facebookarchive/RiftDK2/Headset/Optical/DK2_Optical_Design.pdf

# DK2 Optical Design

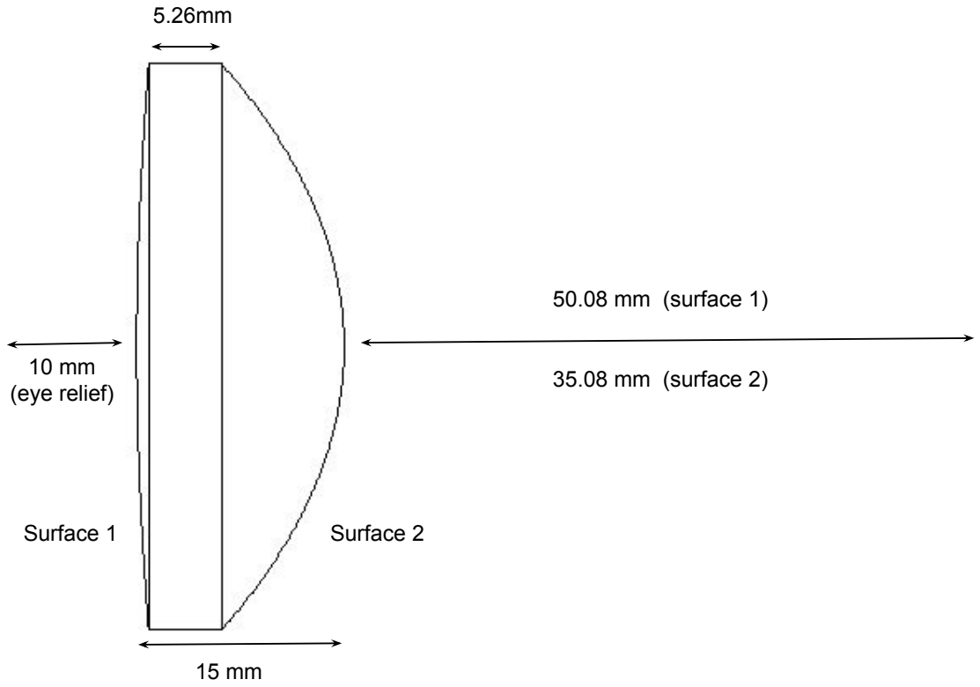
[picture p18: figure]
Surface 1; Surface 2; 10 mm (eye relief); 50.08 mm (surface 1); 35.08 mm (surface 2)

Material: Polycarbonate
Surface 1: radius = 20.457 mm, curvature radius = 212.774, conic = -60.6277 Surface 2: radius = 20.457 mm, curvature radius = -24.2189, conic = -0.863502 Thickness: 15 mm
Stereo Lens Separation: 63.5 mm
Active Screen Size: 125.76 x 70.74 mm (1920 x 1080 pixels)
Optical Center Screen Position: Left = (31.13, 35.37) mm | Right = (94.63, 35.37) mm ⁴⁰.914 mm

Active screen (not including front glass)
