facebookarchive/RiftDK2/Documentation/Figures/image6-25.png

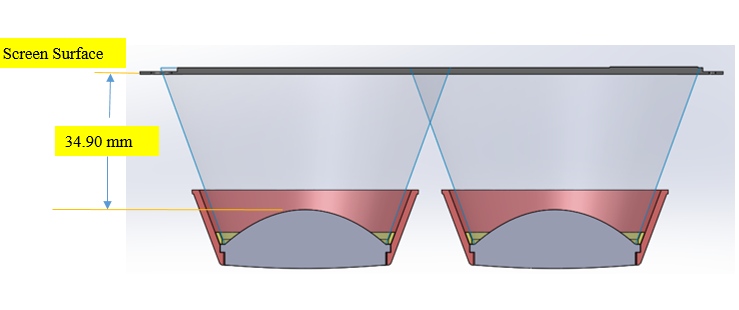
Documentation/Figures/image6-25.png
