facebookarchive/RiftDK2/Headset/Artwork/DK2 artwork placement Development Kit 2.PDF

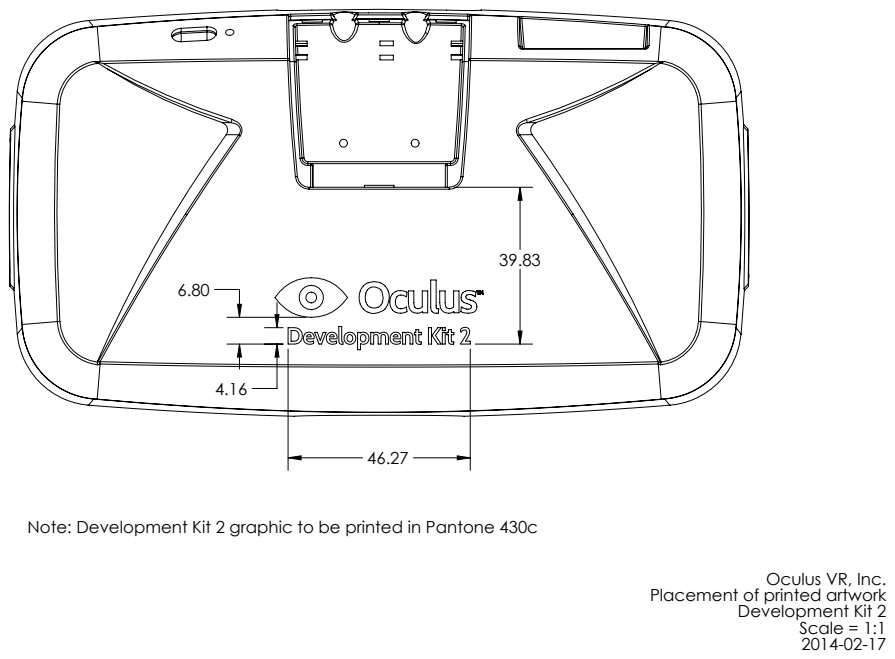
[picture p43: page 1]

Note: Development Kit 2 graphic to be printed in Pantone 430c

Oculus VR, Inc.
Development Kit 2
Scale = 1:1

Placement of printed artwork
