facebookarchive/RiftDK2/Headset/Artwork/DK2 master carton 2014-06-12.pdf

834 | 313

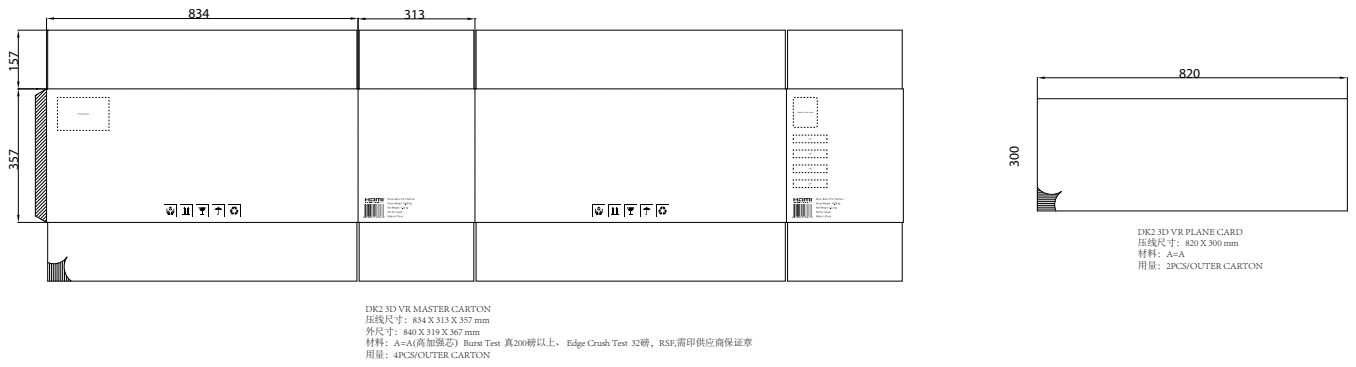
[picture p44: page 1]

DK2 3D VR PLANE CARD
压线尺寸：820 X 300 mm
用量：2PCS/OUTER CARTON

DK2 3D VR MASTER CARTON
压线尺寸：834 X 313 X 357 mm
外尺寸：840 X 319 X 367 mm
材料：A=A(高加强芯）Burst Test 真200磅以上、 Edge Crush Test 32磅，RSF,需印供应商保证章
用量：4PCS/OUTER CARTON
