facebookarchive/RiftDK2/Headset/Artwork/DK2 overpack 2014-06-12.pdf

280.0

295 | 199

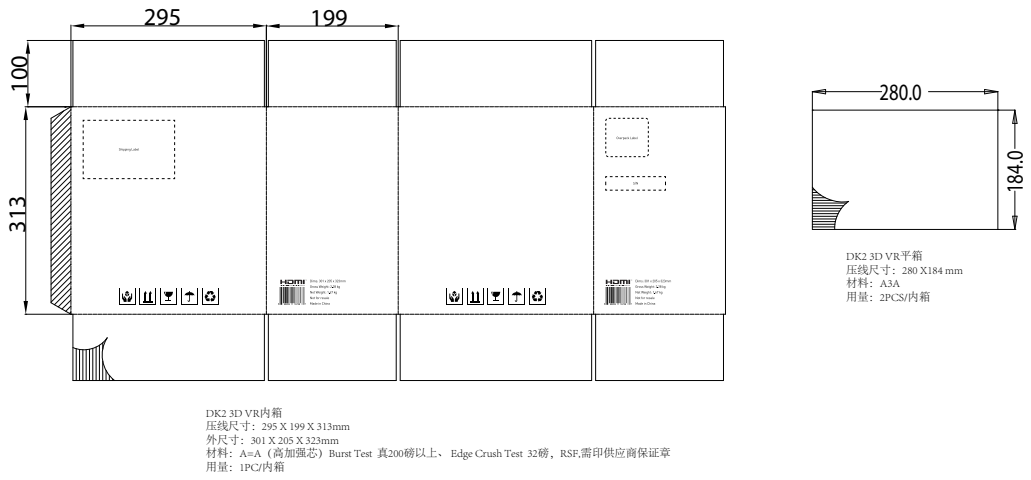
[picture p45: page 1]
DK2 3D VR平箱 压线尺寸：280 X184 mm 材料：A3A 用量：2PCS/内箱

DK2 3D VR内箱
压线尺寸：295 X 199 X 313mm
外尺寸：301 X 205 X 323mm
材料：A=A（高加强芯）Burst Test 真200磅以上、 Edge Crush Test 32磅，RSF,需印供应商保证章
