facebookarchive/RiftDK2/Headset/Artwork/USB-HDMI-Packaging_1.3.pdf

SCALE 200% | ACTUAL SIZE

# DK2: USB / HDMI SILKSCREEN

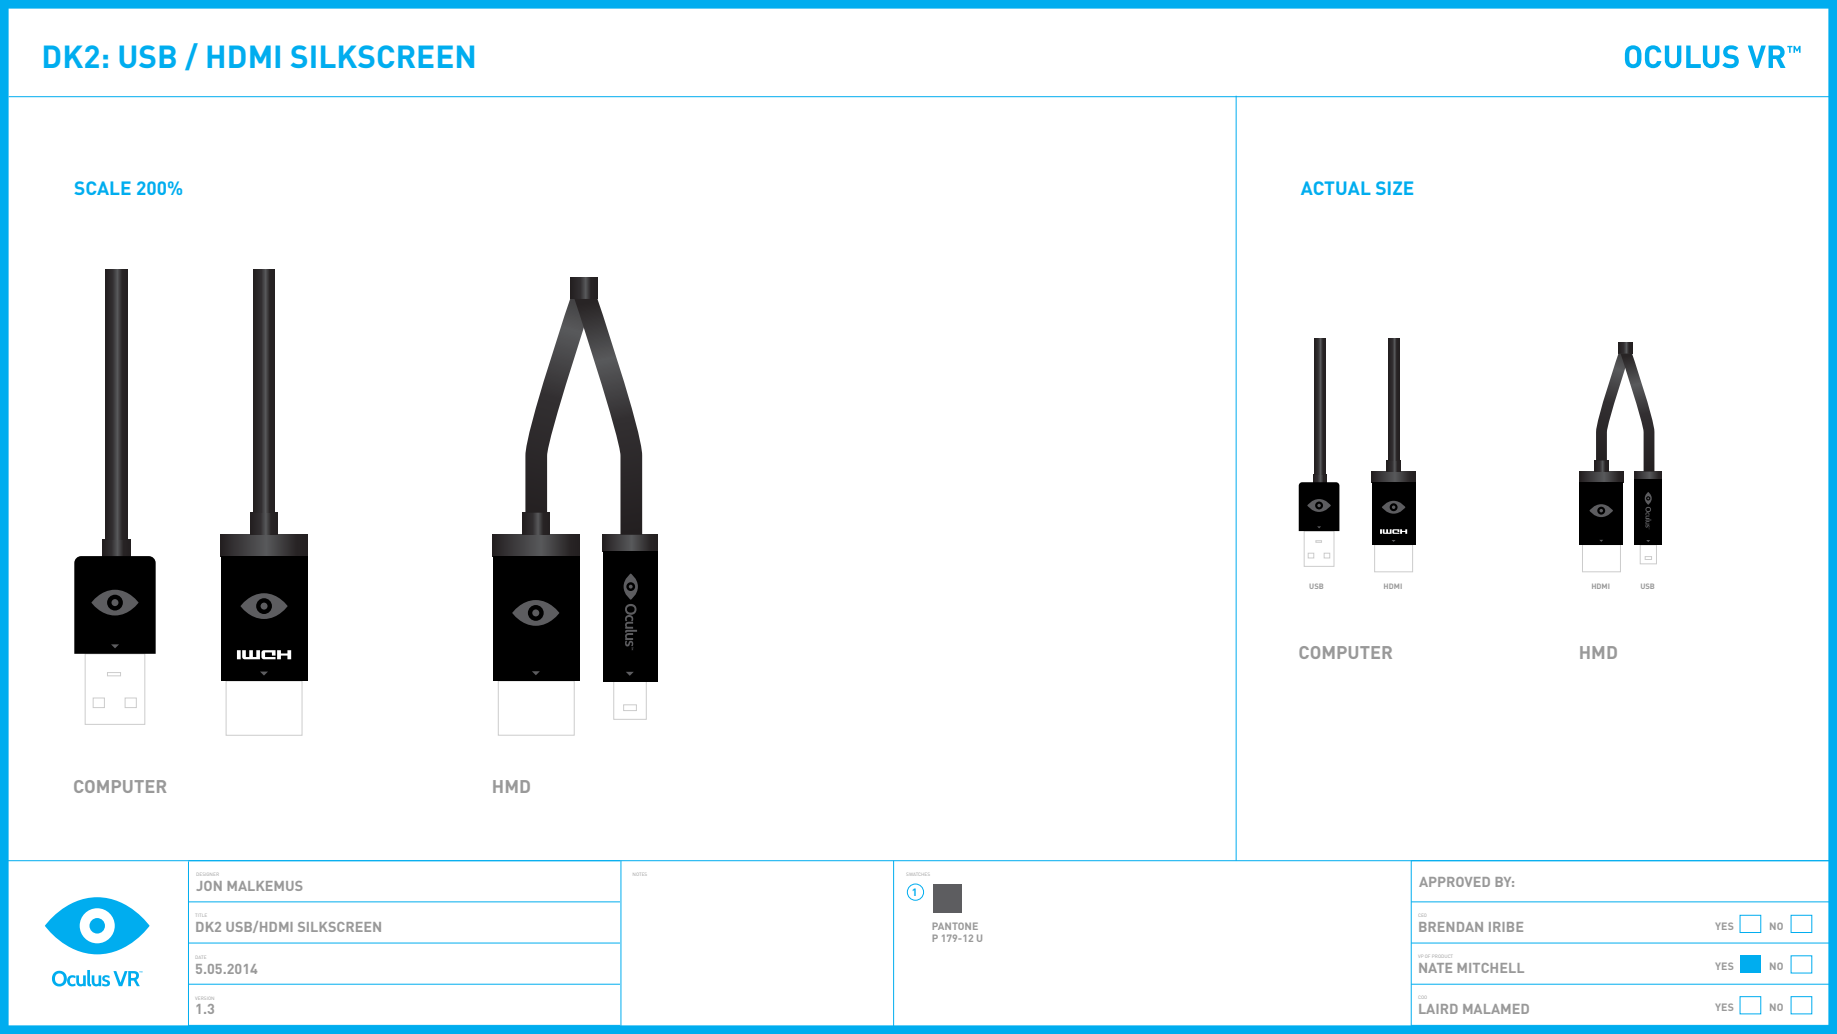
[picture p46: page 1]
COMPUTER; JON MALKEMUS; DESIGNER; NOTES; SWATCHES; DATE; VERSION; APPROVED BY:; BRENDAN IRIBE; YES; CEO; LAIRD MALAMED; COO; HMD; PANTONE P 179-12 U; USB; HDMI

TITLE
DK2 USB/HDMI SILKSCREEN

VP OF PRODUCT
NATE MITCHELL
