facebookarchive/RiftDK2/Headset/Electrical/Mainboard/Release/DK2_REV3.3_SCH.pdf

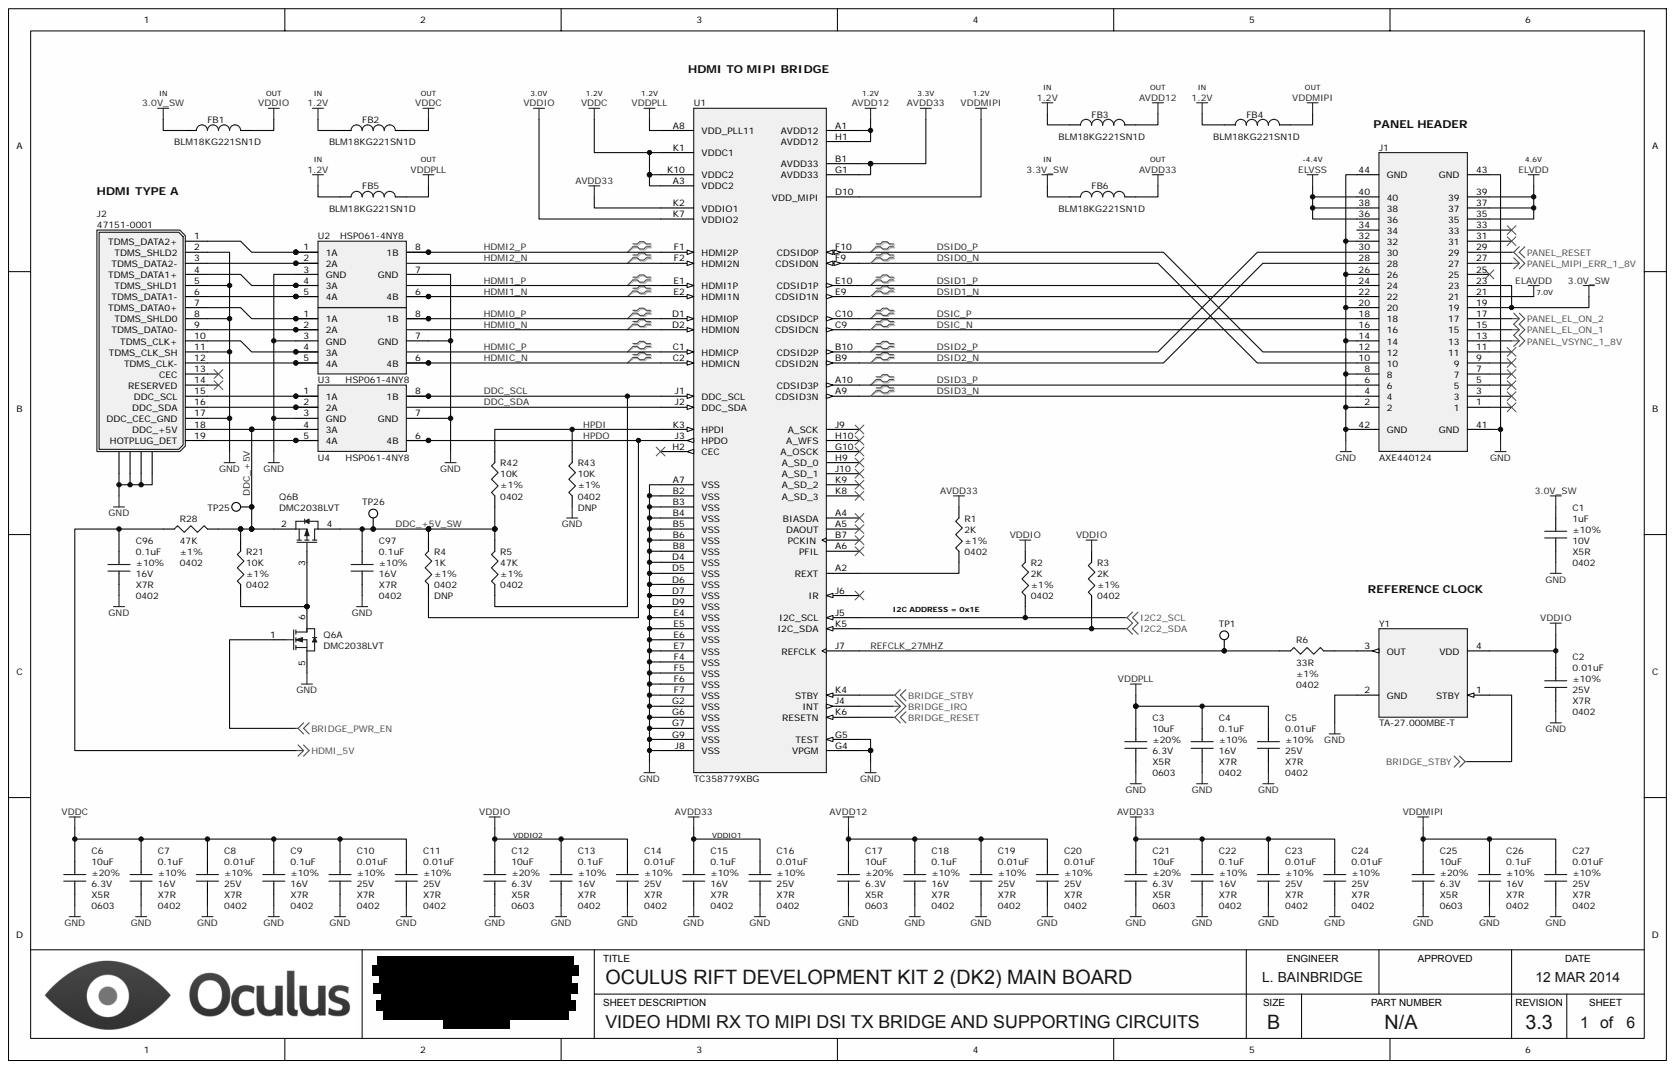
[picture p47: page 1]

HDMI TO MIPI BRIDGE

SHEET DESCRIPTION
VIDEO HDMI RX TO MIPI DSI TX BRIDGE AND SUPPORTING CIRCUITS

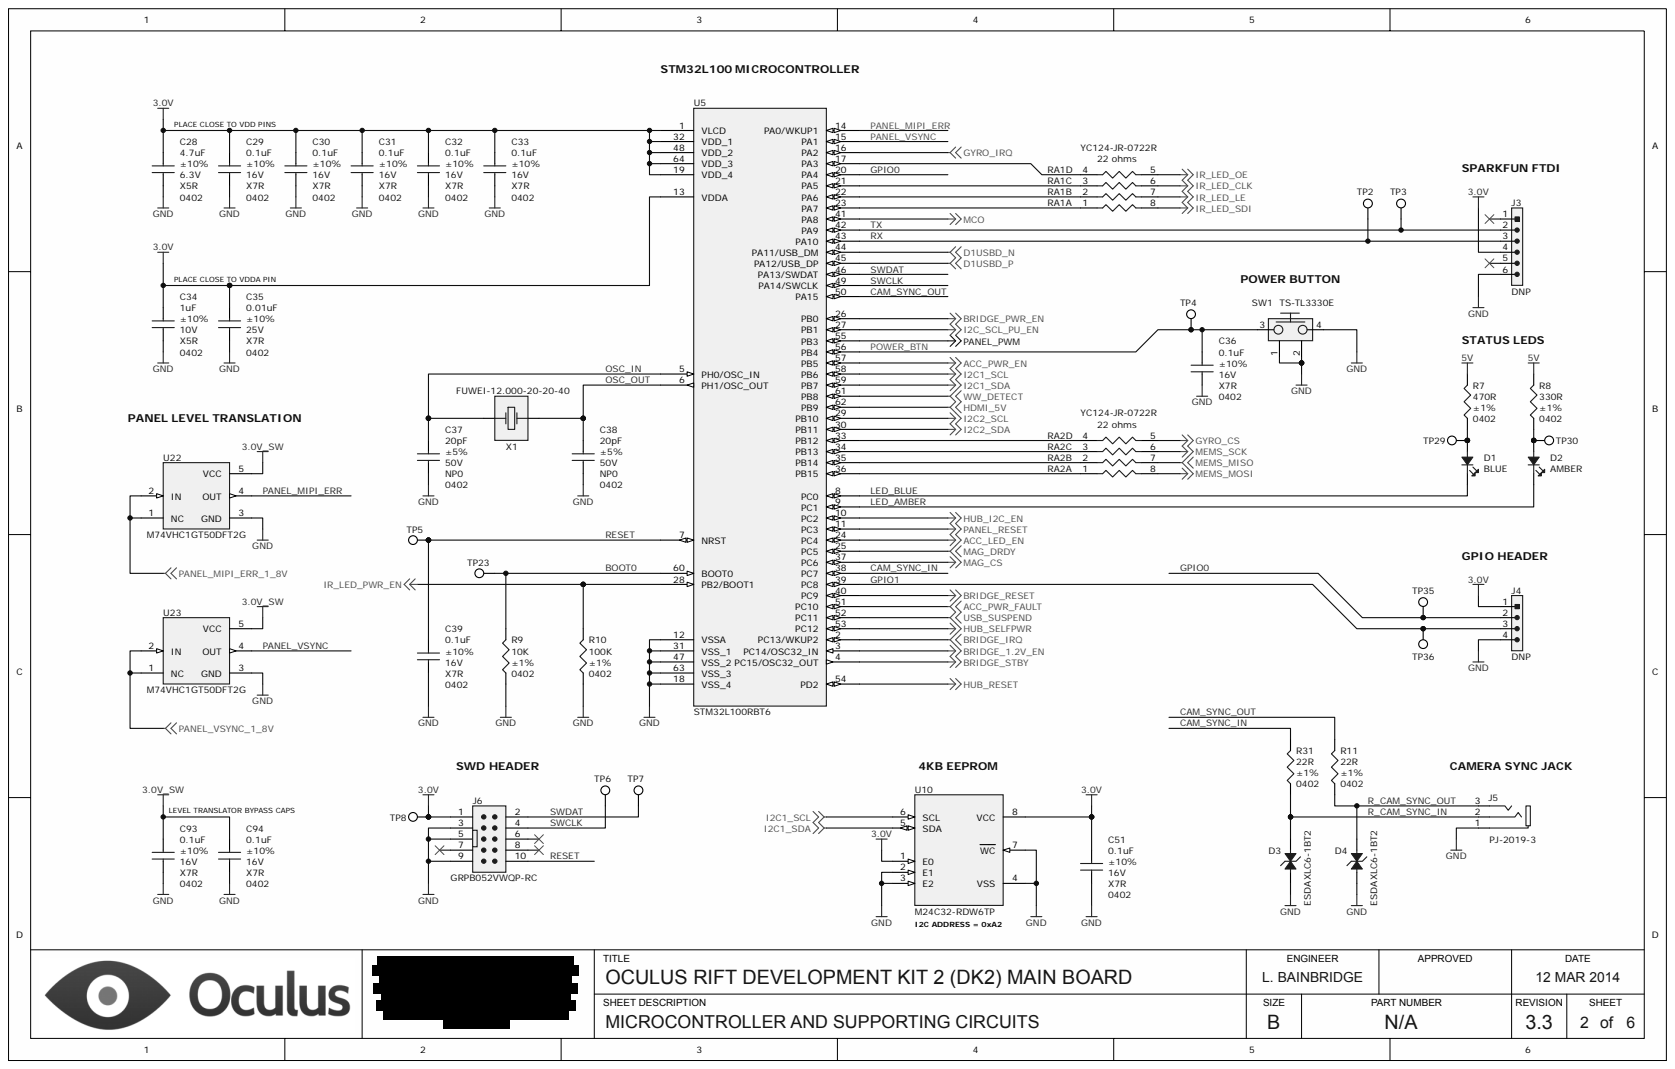
[picture p48: page 2]

MICROCONTROLLER AND SUPPORTING CIRCUITS

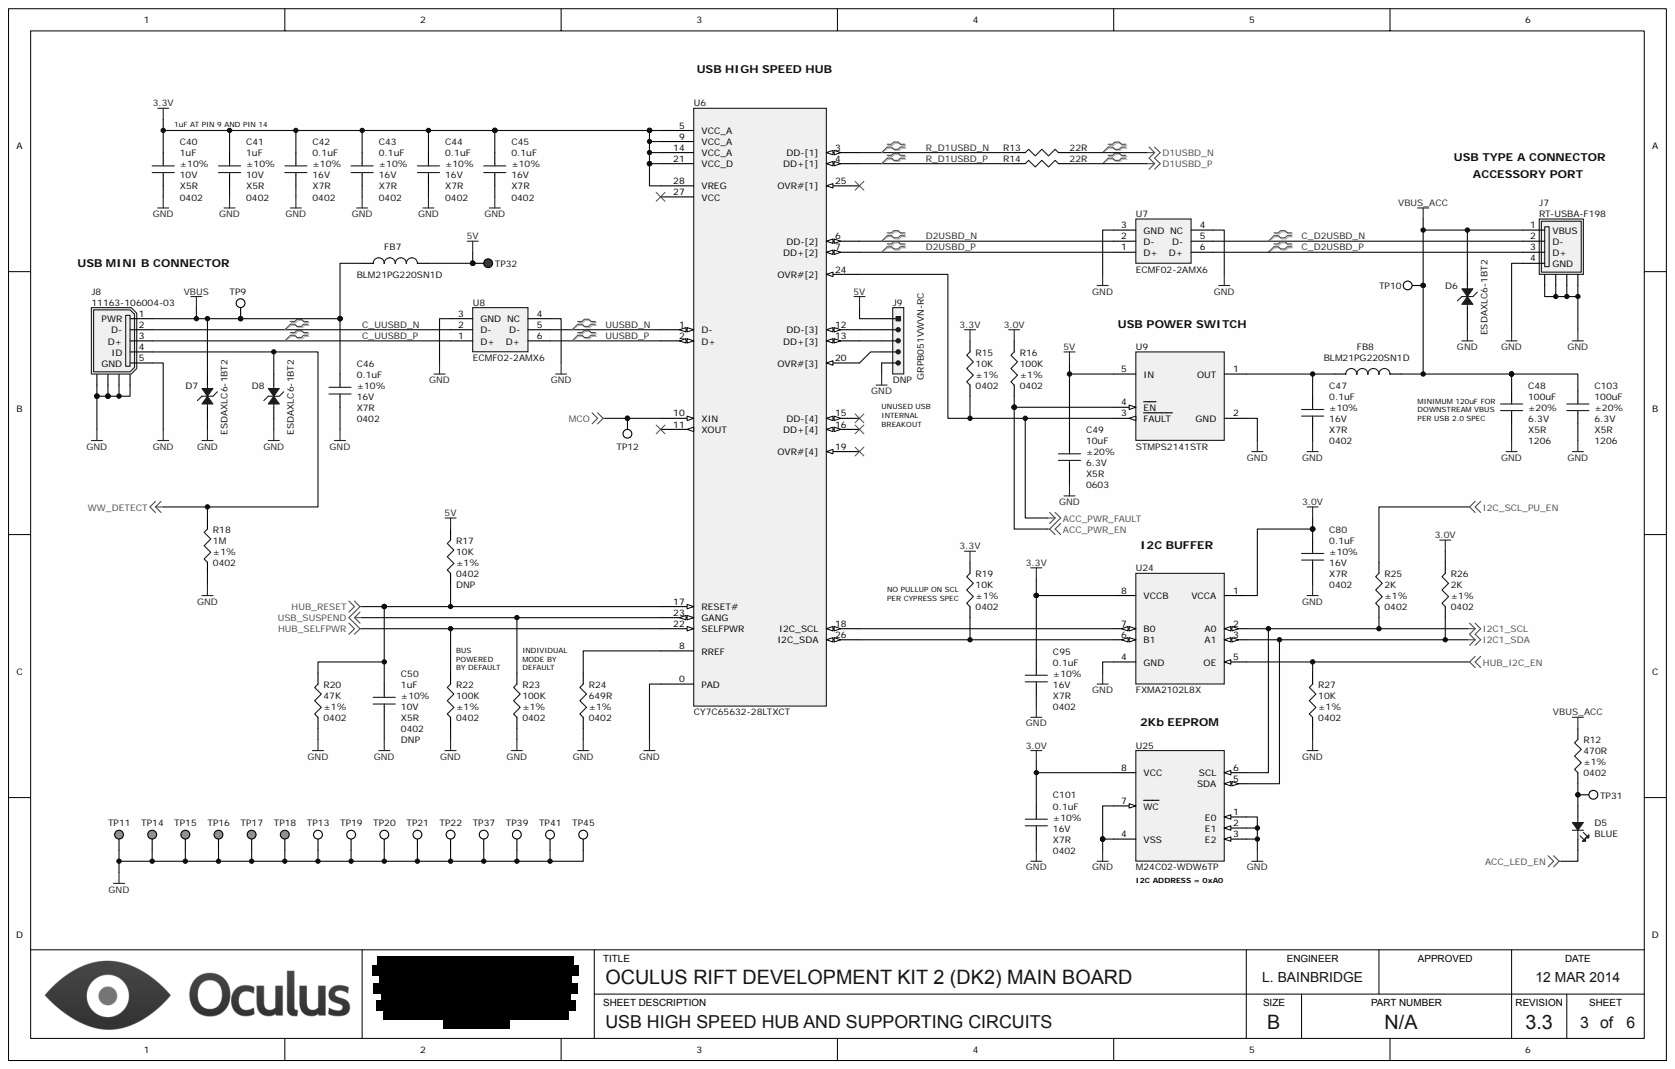
[picture p49: page 3]

USB HIGH SPEED HUB

NO PULLUP ON SCL
PER CYPRESS SPEC

SELFPWR 22 GANG 23

RREF 8 PAD 0

USB HIGH SPEED HUB AND SUPPORTING CIRCUITS

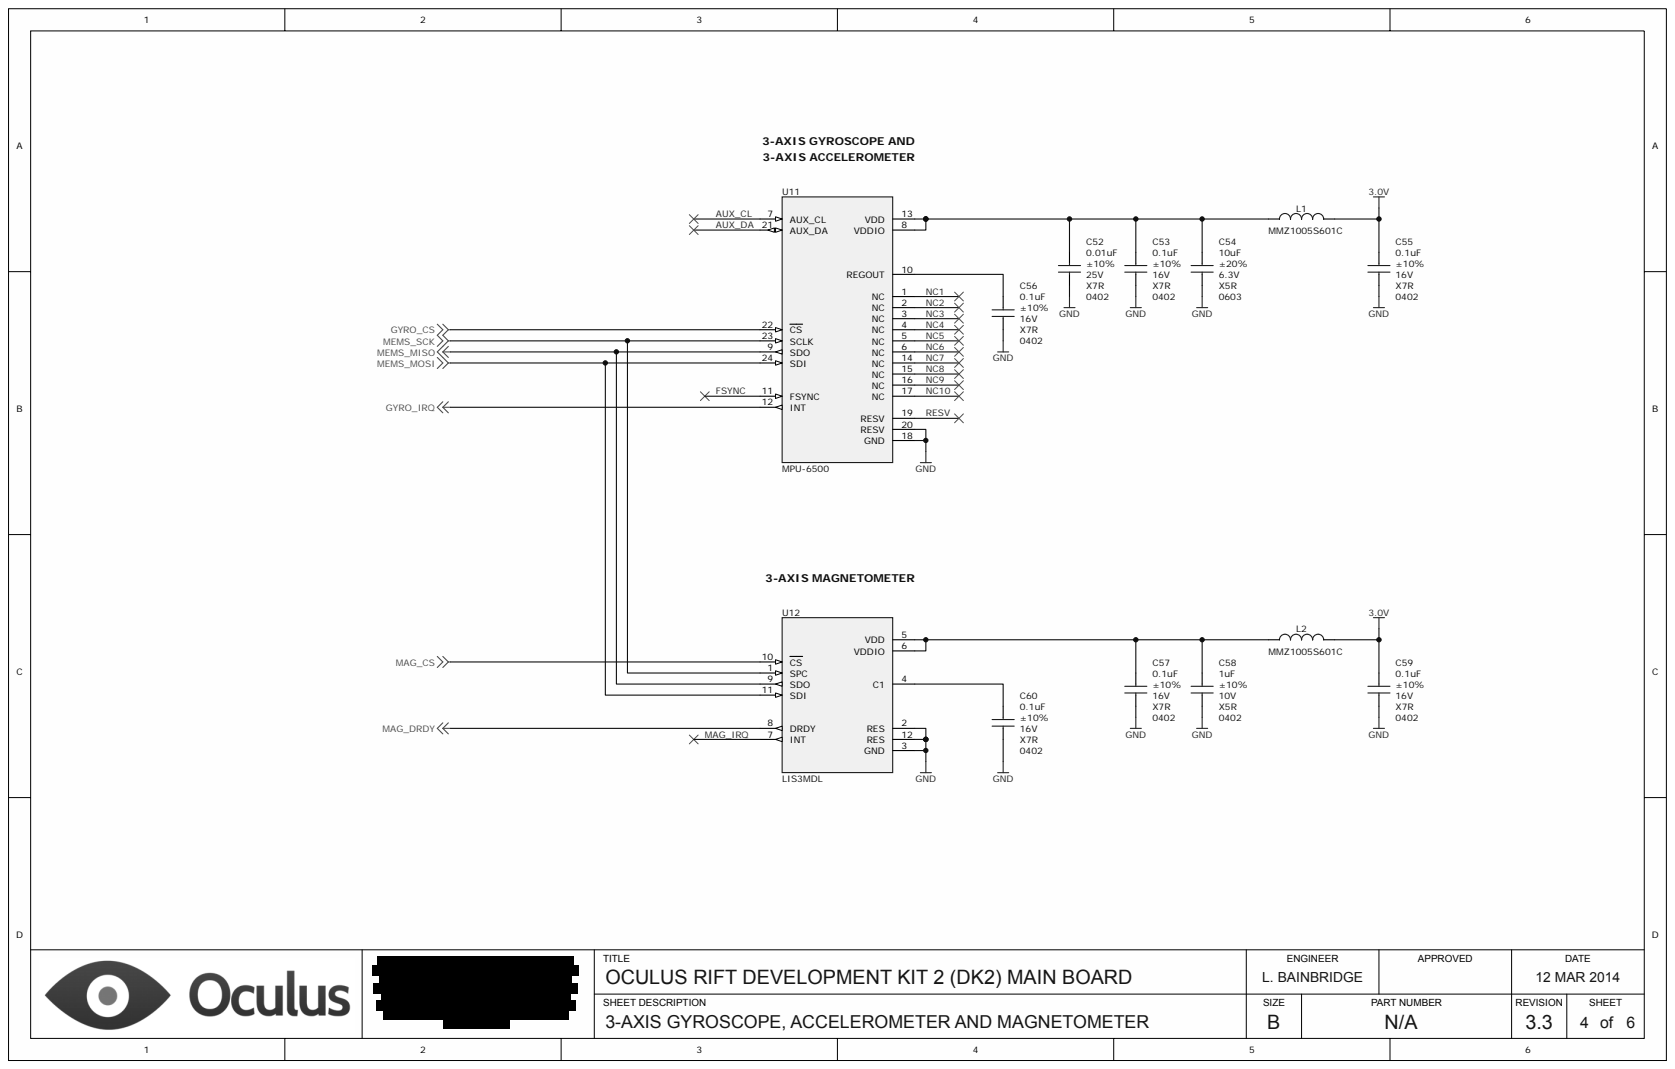
[picture p50: page 4]

3-AXIS GYROSCOPE, ACCELEROMETER AND MAGNETOMETER

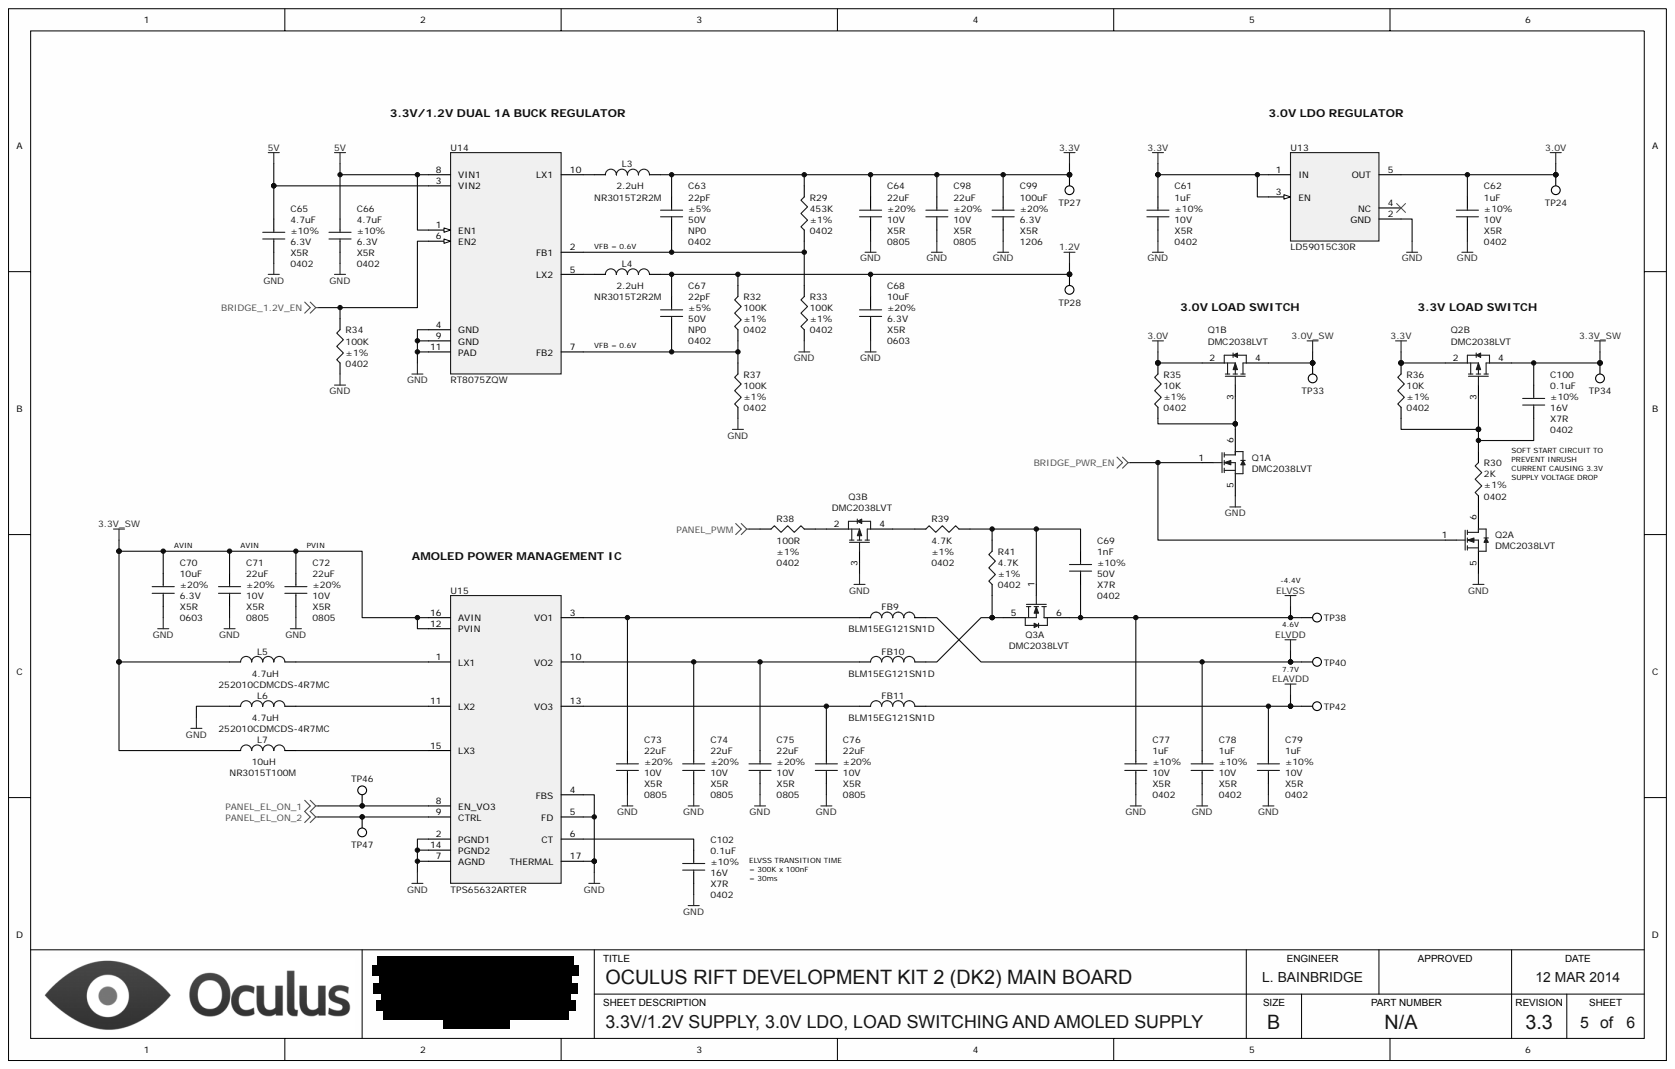
[picture p51: page 5]

AMOLED POWER MANAGEMENT IC

3.3V/1.2V SUPPLY, 3.0V LDO, LOAD SWITCHING AND AMOLED SUPPLY

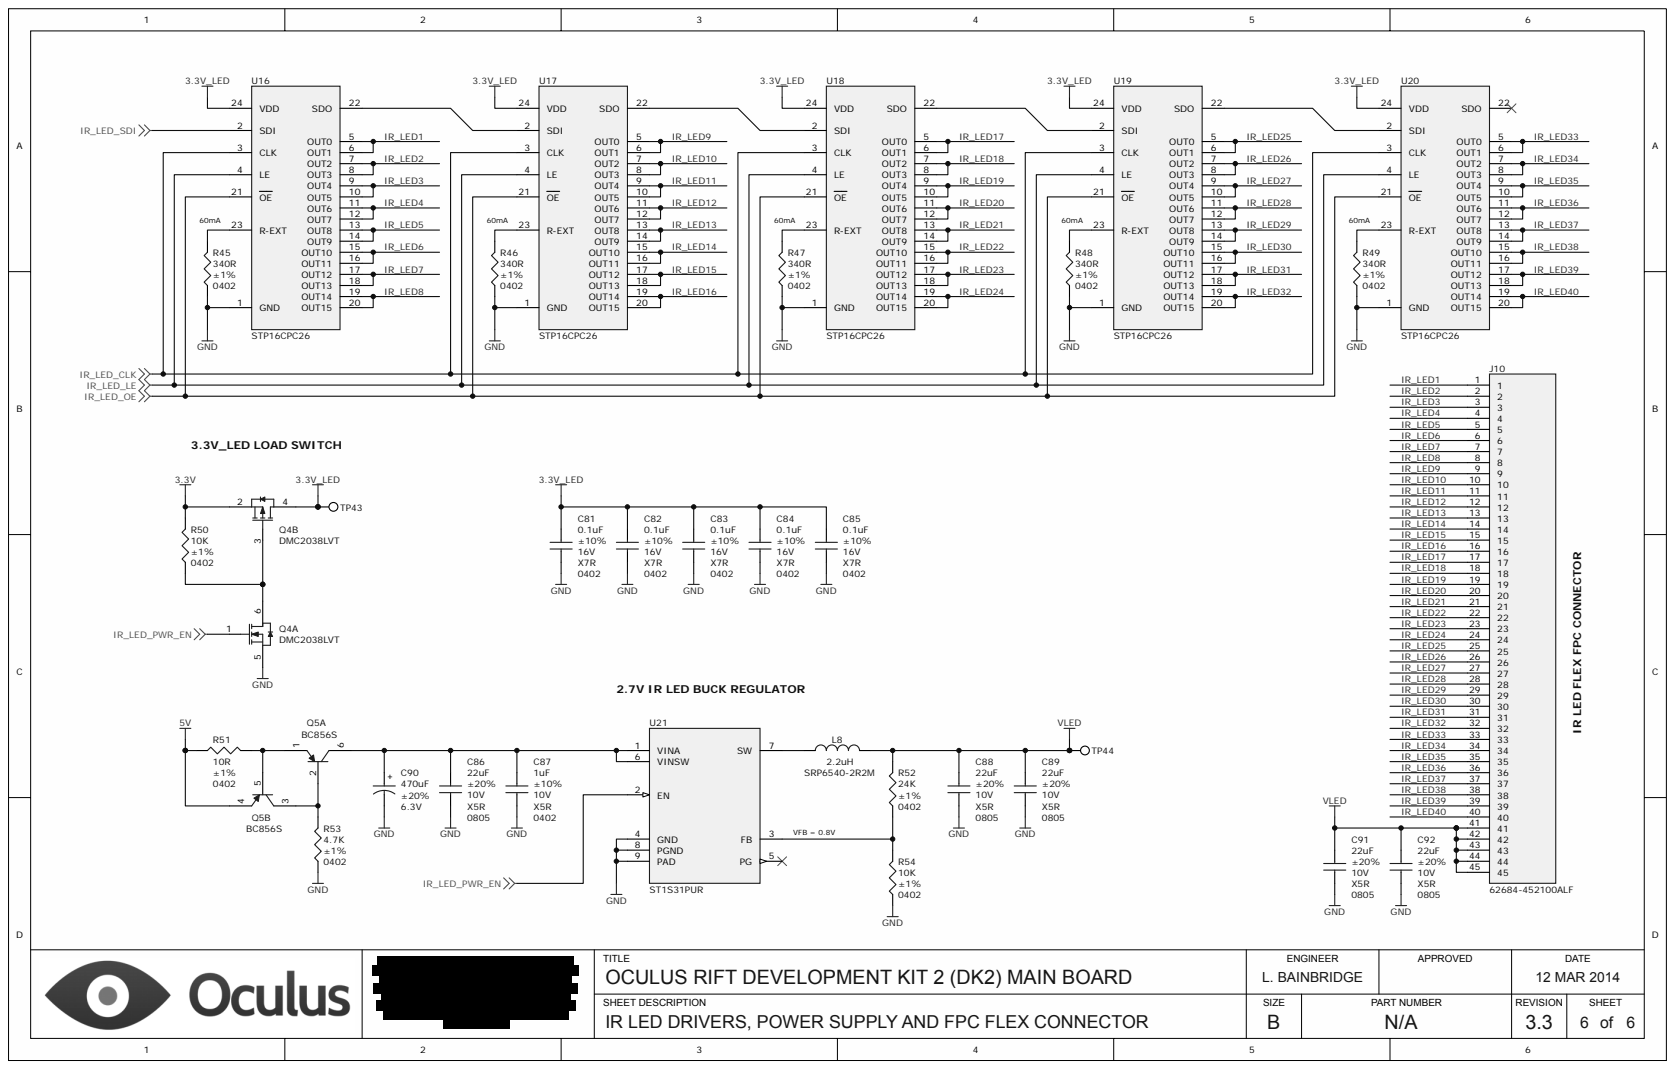
[picture p52: page 6]

IR LED FLEX FPC CONNECTOR

2.7V IR LED BUCK REGULATOR

IR LED DRIVERS, POWER SUPPLY AND FPC FLEX CONNECTOR
