facebookarchive/RiftDK2/Headset/Electrical/Mainboard/Release/DK2_REV3.3_STACKUP.pdf

## Stackup Report

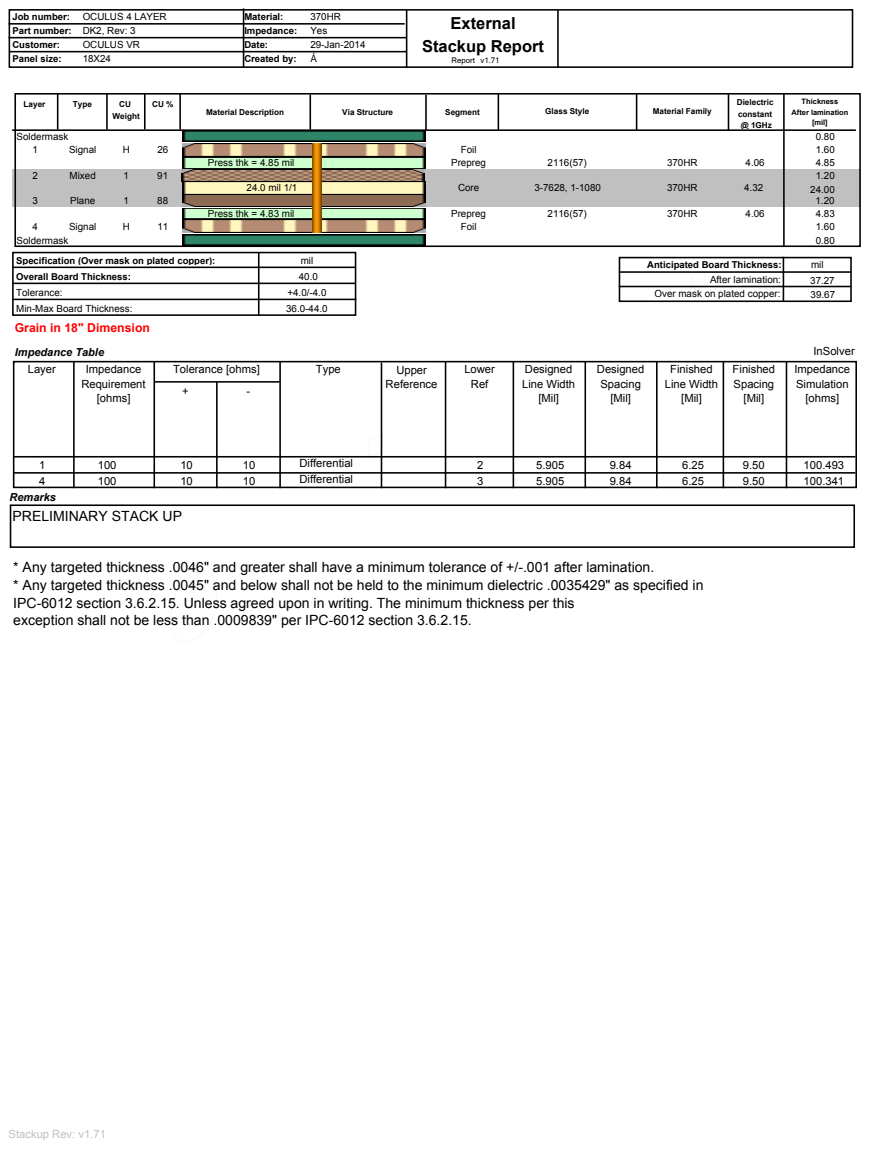
[picture p53: page 1]
Part number:; Date: Created by:; Customer:; 29-Jan-2014; Job number:; Material:; External; OCULUS 4 LAYER; OCULUS VR; Panel size:; DK2, Rev: 3; Impedance:; Yes; Report v1.71; Dielectric constant @ 1GHz; Material Description; Via Structure; Glass Style; Material Family; Layer; Type; Segment; Weight; Thickness After lamination [mil]; Soldermask; Signal; Foil; Press thk = 4.85 mil; Prepreg; Mixed; 24.0 mil 1/1; Core; Plane; Press thk = 4.83 mil; mil 40.0; After lamination:; mil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

Specification (Over mask on plated copper):
Overall Board Thickness:
Tolerance:
Min-Max Board Thickness:
Grain in 18'' Dimension

Anticipated Board Thickness:

Remarks
PRELIMINARY STACK UP

* Any targeted thickness .0046" and greater shall have a minimum tolerance of +/-.001 after lamination.
* Any targeted thickness .0045" and below shall not be held to the minimum dielectric .0035429" as specified in
IPC-6012 section 3.6.2.15. Unless agreed upon in writing. The minimum thickness per this
exception shall not be less than .0009839" per IPC-6012 section 3.6.2.15.
