facebookarchive/RiftDK2/Sensor/Electrical/IR Sync/Release/0008-NSA_IR_Sync_Board.PDF

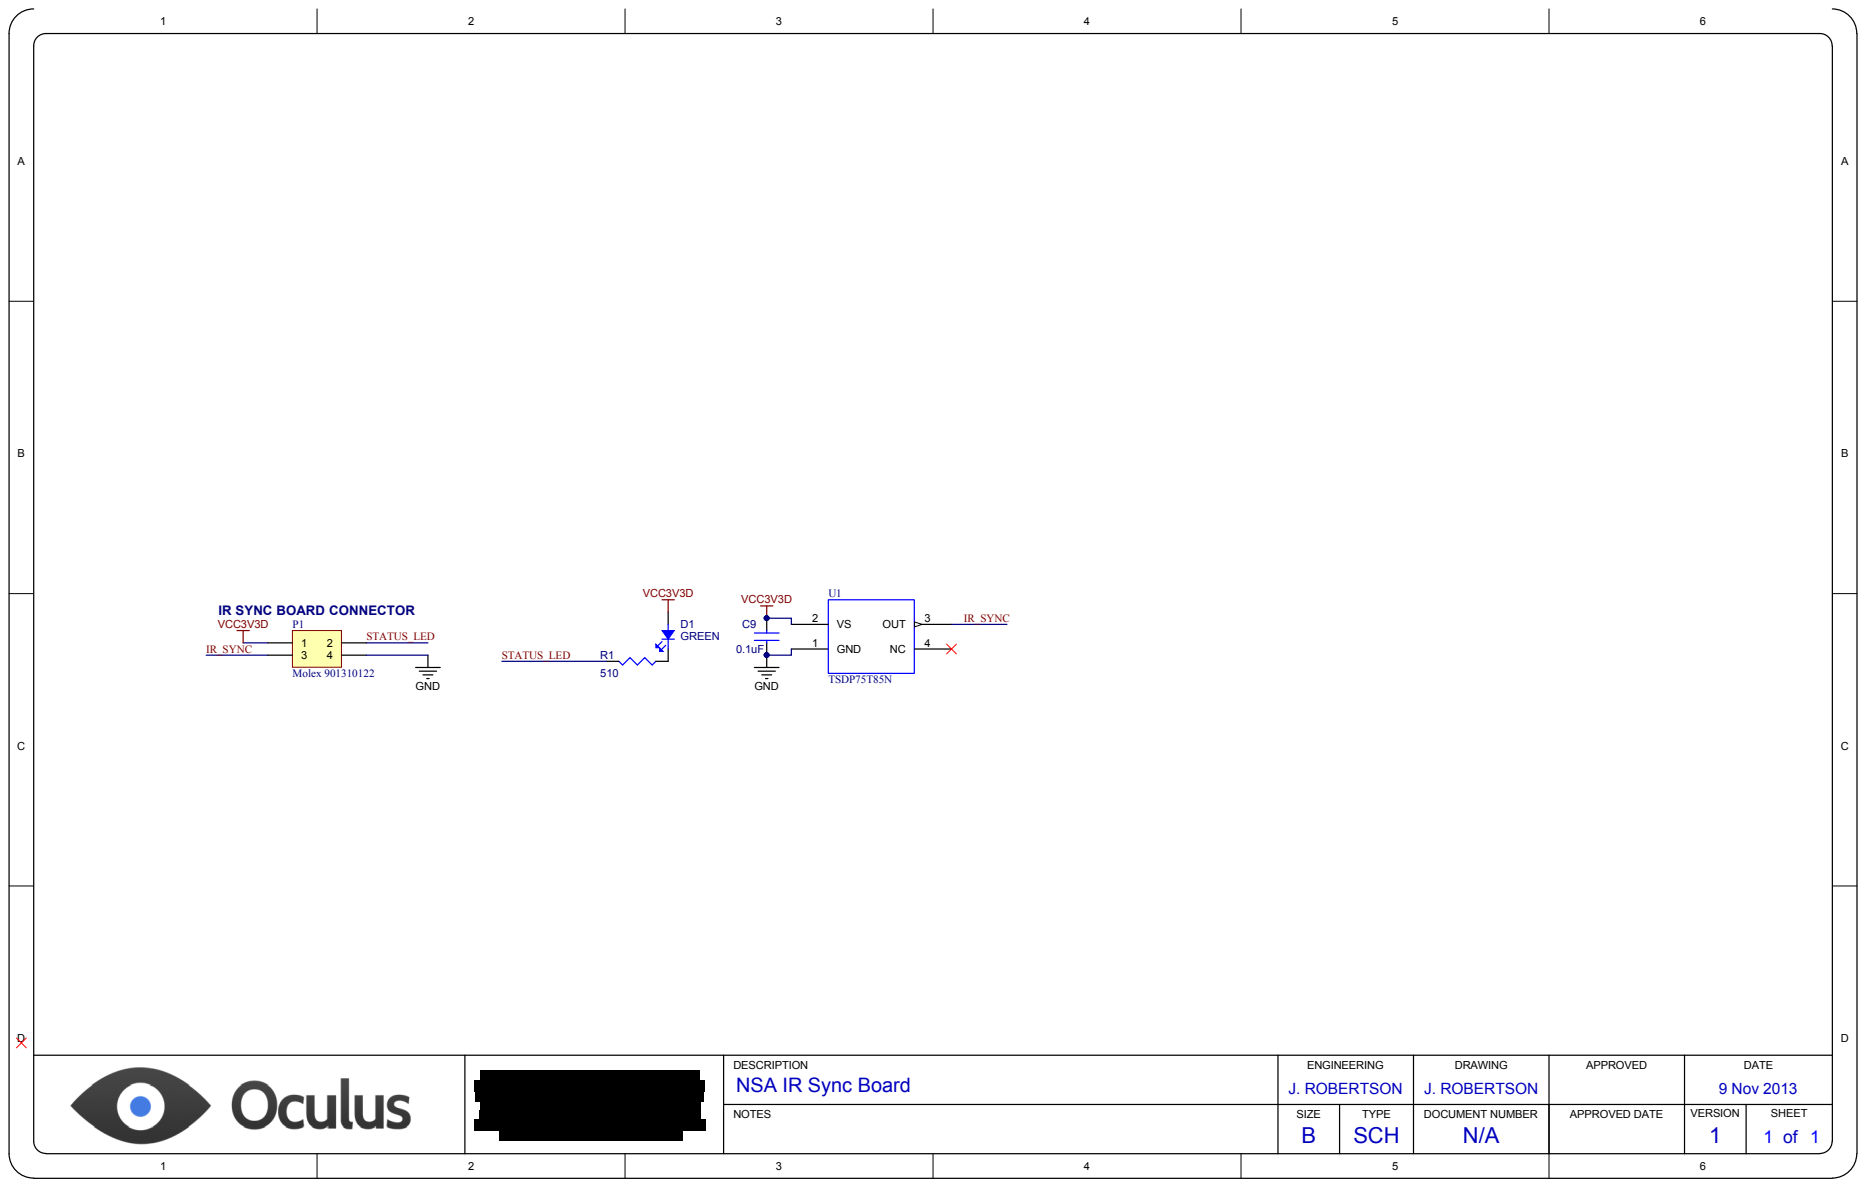
[picture p54: page 1]
NOTES; SHEET; VERSION 1; DATE 9 Nov 2013; ENGINEERING; J. ROBERTSON; DRAWING; APPROVED; SIZE; DOCUMENT NUMBER; SCH; TYPE; APPROVED DATE; GREEN; VCC3V3D; GND; OUT; TSDP75T85N; IR_SYNC; STATUS_LED; Molex 901310122

IR SYNC BOARD CONNECTOR
VCC3V3D

NSA IR Sync Board DESCRIPTION
