facebookarchive/RiftDK2/Headset/Artwork/DK2 product label HMD.pdf

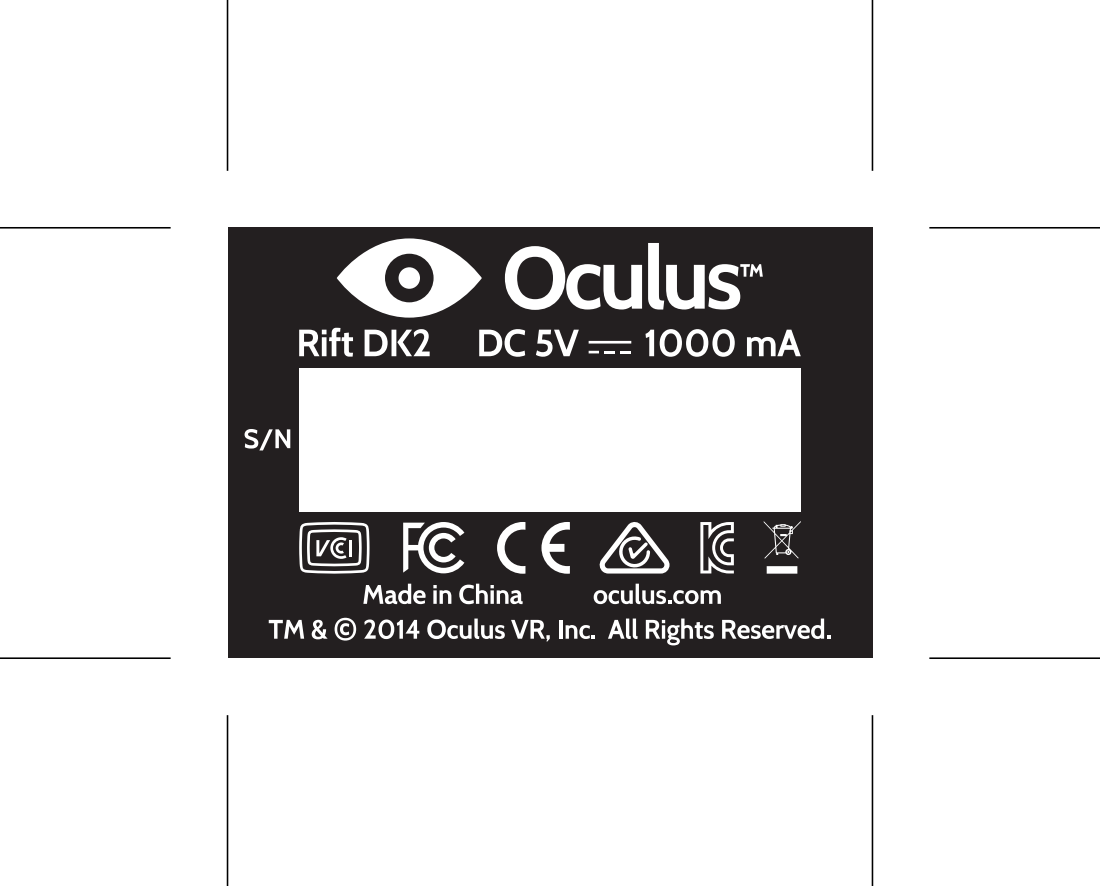
[picture p58: page 1]
