facebookarchive/RiftDK2/Headset/Artwork/DK2 product package 2014-06-09.pdf

## FRONT

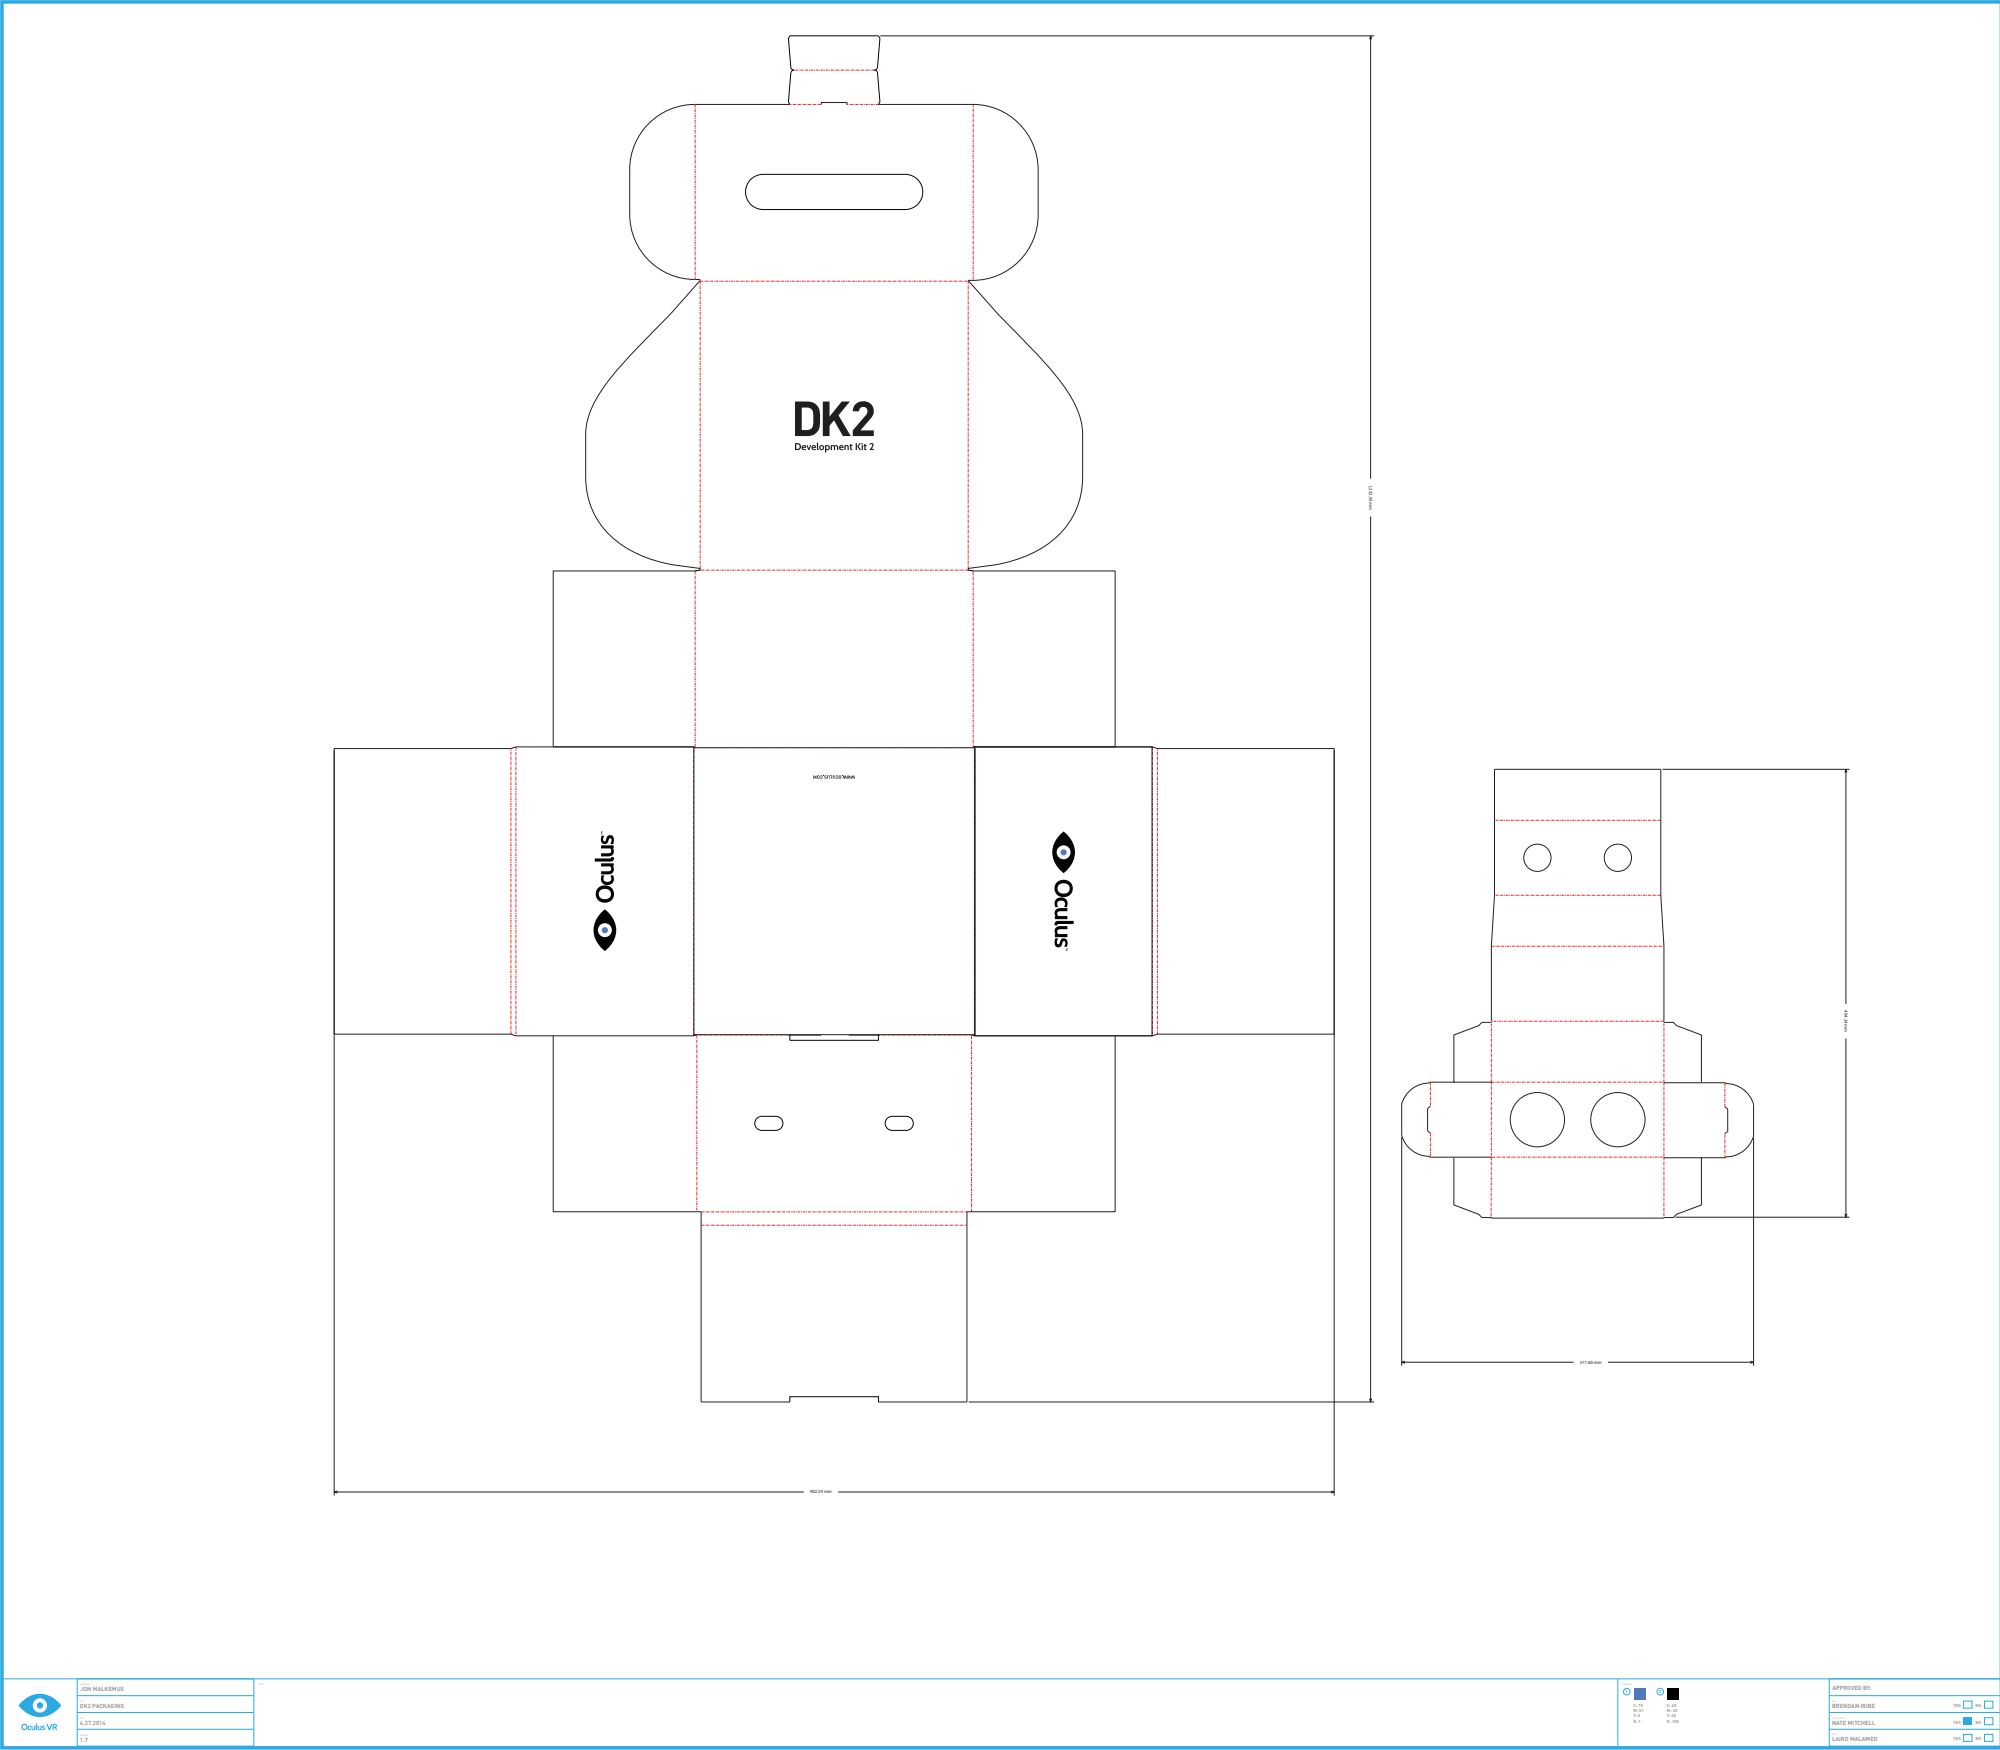
[picture p59: page 1]
BOTTOM

DESIGNER JON MALKEMUS | NOTES | SWATCHES 1 2 C: 72 C: 60 M: 51 M: 40 Y: 0 Y: 40 K: 1 K: 100 | APPROVED BY:

TITLE DK2 PACKAGING | | | CEO BRENDAN IRIBE YES NO

DATE 4.27.2014 | | | VP OF PRODUCT NATE MITCHELL YES NO

VERSION 1.7 | | | COO LAIRD MALAMED YES NO
