facebookarchive/RiftDK2/Headset/Artwork/DK2 shipping label master carton 2014-06-09.pdf

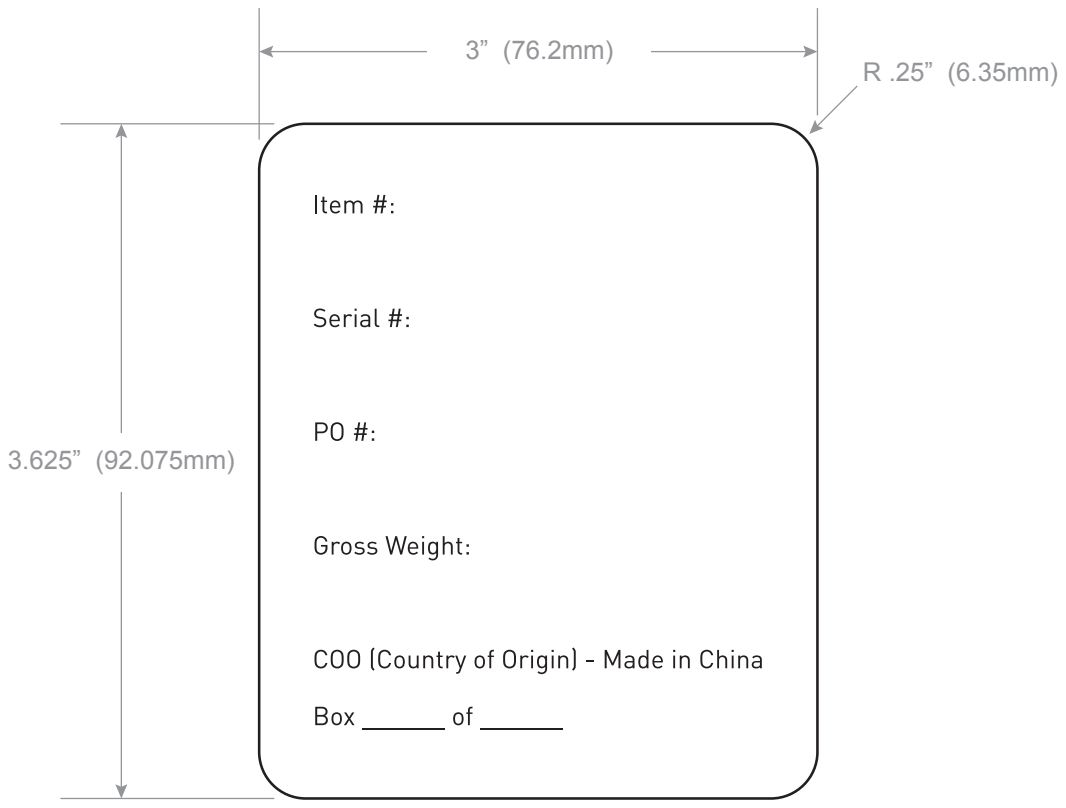
[picture p60: page 1]
