facebookarchive/RiftDK2/Headset/Artwork/DK2 shipping label overpack 2014-06-09.pdf

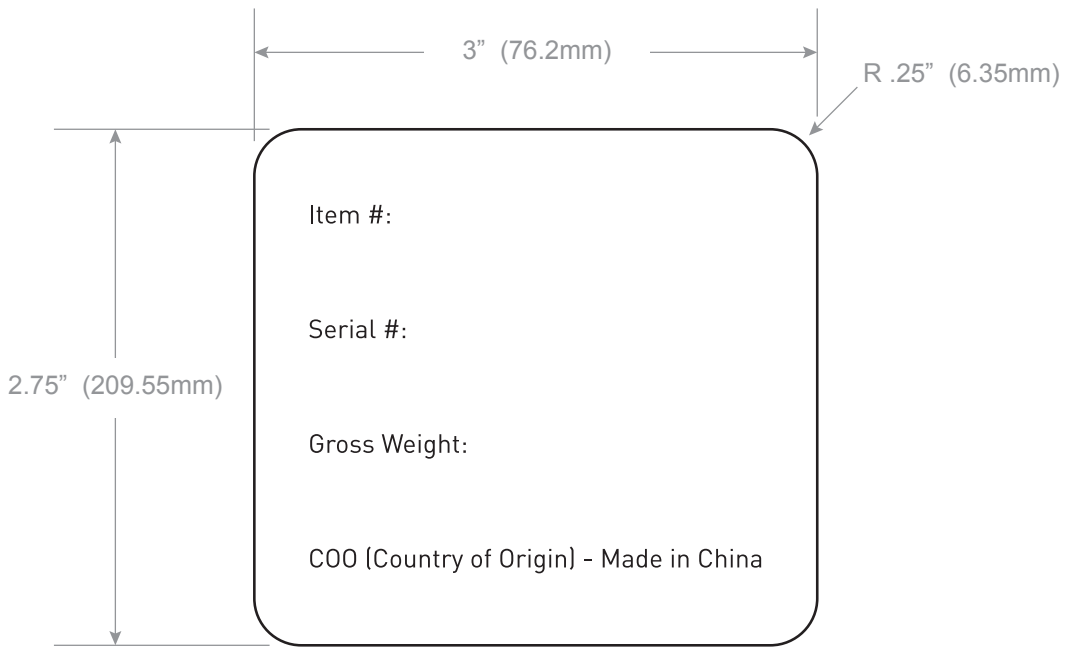
[picture p61: page 1]
