facebookarchive/RiftDK2/Headset/Artwork/Oculus wipe cloth DK2.pdf

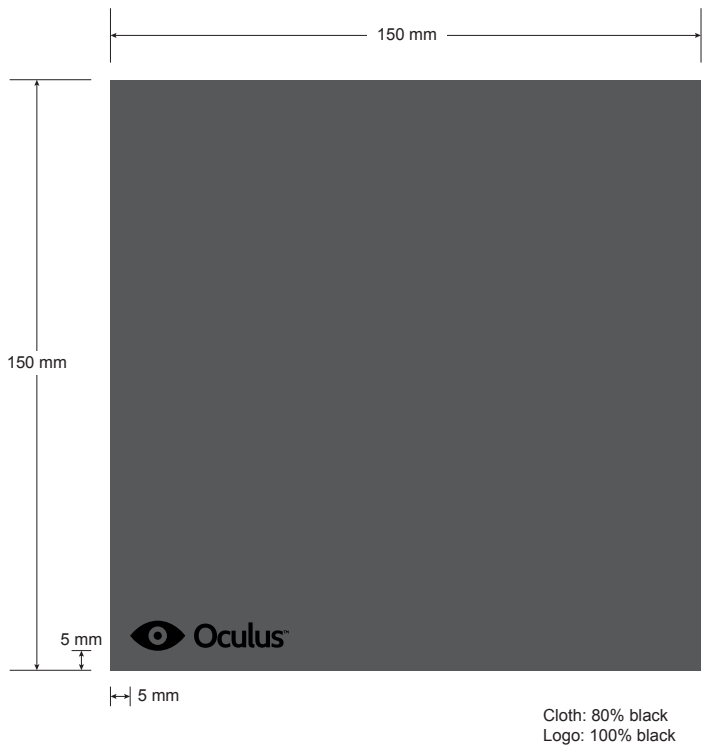
[picture p62: page 1]
Cloth: 80% black Logo: 100% black
