facebookarchive/RiftDK2/Sensor/Artwork/DK2 product label Camera.pdf

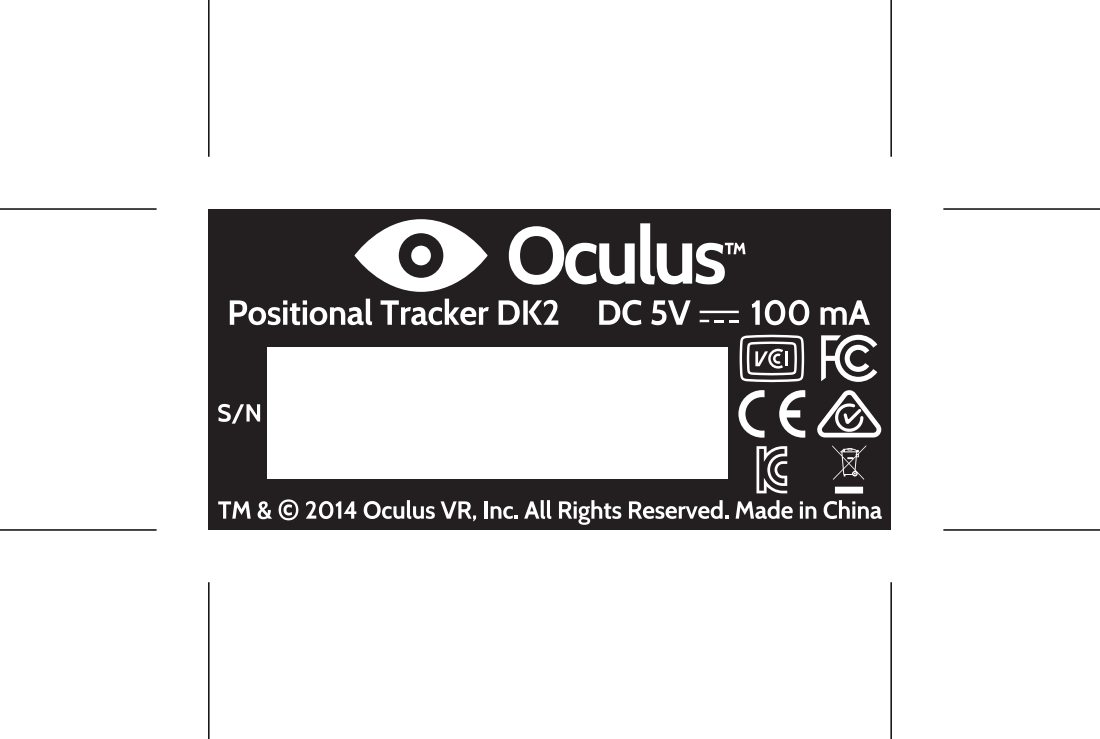
[picture p63: page 1]
